SunRichardSKT/ai-doll-mcp/tools/companion.py

"""Persistent touch archive and interaction sessions. Device transport is injected."""
import datetime as dt
import json
import sqlite3
import threading
import time
import uuid
import re
import sys
from contextlib import contextmanager
from importlib.metadata import version as package_version, PackageNotFoundError
from interaction_bridge import EventBridge
from input_observations import pressure_observations


def utcnow():
    return time.time()


class DeviceBusyError(TimeoutError):
    """An operation was not started because the device connection is occupied."""


@contextmanager
def bounded_device_lock(lock):
    # A waiting HTTP/MCP request must expire before it becomes a late output.
    # This bounds queue time, not the transport's own in-flight network timeout.
    if not lock.acquire(timeout=2):
        raise DeviceBusyError('Device connection busy; operation was not started')
    try:
        yield
    finally:
        lock.release()


class Companion:
    def __init__(self, path, exchange, serial_lock):
        self.exchange, self.serial_lock = exchange, serial_lock
        self.lock = threading.RLock()
        self.db = sqlite3.connect(path, check_same_thread=False)
        self.db.row_factory = sqlite3.Row
        self.db.executescript('''
        PRAGMA journal_mode=WAL;
        CREATE TABLE IF NOT EXISTS settings(key TEXT PRIMARY KEY,value TEXT NOT NULL);
        CREATE TABLE IF NOT EXISTS boots(device TEXT,boot TEXT,offset REAL,cursor INTEGER,
          PRIMARY KEY(device,boot));
        CREATE TABLE IF NOT EXISTS sessions(id TEXT PRIMARY KEY,chat_id TEXT,started REAL,
          ended REAL,last_activity REAL,timeout INTEGER,reason TEXT);
        CREATE TABLE IF NOT EXISTS session_boundaries(session_id TEXT PRIMARY KEY,
          device TEXT,boot TEXT,seq INTEGER);
        CREATE TABLE IF NOT EXISTS session_limits(session_id TEXT PRIMARY KEY,deadline REAL NOT NULL);
        CREATE TABLE IF NOT EXISTS touches(id INTEGER PRIMARY KEY AUTOINCREMENT,
          device TEXT,touch_id TEXT,channel INTEGER,body_part TEXT,source TEXT,
          started REAL,ended REAL,duration_ms INTEGER,peak_raw INTEGER,session_id TEXT,
          UNIQUE(device,touch_id));
        CREATE TABLE IF NOT EXISTS events(id INTEGER PRIMARY KEY AUTOINCREMENT,
          device TEXT,boot TEXT,seq INTEGER,at REAL,payload TEXT,
          UNIQUE(device,boot,seq));
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
